andrewgreenwood/scrapbrain/src/panel/graphics.h

#ifndef SCRAPBRAIN_GRAPHICS_H
#define SCRAPBRAIN_GRAPHICS_H 1

#define BACKGROUND_COLOUR           0x1082
#define TOPBAR_COLOUR               0x0000
#define CARRIER_OPERATOR_COLOUR     0x2589
#define MODULATOR_OPERATOR_COLOUR   0xf3e4
#define OPERATOR_LINK_COLOUR        0xffff

#define INDICATOR_OUTLINE_COLOUR    0xffff
#define GREEN_INDICATOR_COLOUR      0x2589
#define GREEN_INDICATOR_LOW_COLOUR  0x0000

#define BUTTON_OUTLINE_COLOUR       BACKGROUND_COLOUR
// 0x0841

enum {
    GRAPHIC_INDICATOR_OUTLINE = GRAPHIC_FIRST_ID,
    GRAPHIC_GREEN_INDICATOR,
    GRAPHIC_ALGORITHM_BUTTON_OUTLINE,
    GRAPHIC_CARRIER_OPERATOR_SQUARE,
    GRAPHIC_BIG_CARRIER_OPERATOR_SQUARE,
    GRAPHIC_MODULATOR_OPERATOR_SQUARE,
    GRAPHIC_BIG_MODULATOR_OPERATOR_SQUARE,
    GRAPHIC_VERTICAL_OPERATOR_CONNECTION,
    GRAPHIC_BIG_VERTICAL_OPERATOR_CONNECTION,
    GRAPHIC_UP_LEFT_OPERATOR_CONNECTION,
    GRAPHIC_BIG_UP_LEFT_OPERATOR_CONNECTION,
    GRAPHIC_UP_RIGHT_OPERATOR_CONNECTION,
    GRAPHIC_BIG_UP_RIGHT_OPERATOR_CONNECTION,
    GRAPHIC_LEFT_UP_OPERATOR_CONNECTION,
    GRAPHIC_BIG_LEFT_UP_OPERATOR_CONNECTION,
    GRAPHIC_RIGHT_UP_OPERATOR_CONNECTION,
    GRAPHIC_BIG_RIGHT_UP_OPERATOR_CONNECTION,
    GRAPHIC_ALGORITHM_1_SMALL,
    GRAPHIC_ALGORITHM_1_BIG,
    GRAPHIC_ALGORITHM_2_SMALL,
    GRAPHIC_ALGORITHM_2_BIG,
    GRAPHIC_ALGORITHM_3_SMALL,
    GRAPHIC_ALGORITHM_3_BIG,
    GRAPHIC_ALGORITHM_4_SMALL,
    GRAPHIC_ALGORITHM_4_BIG,
    GRAPHIC_ALGORITHM_5_SMALL,
    GRAPHIC_ALGORITHM_5_BIG,
    GRAPHIC_ALGORITHM_6_SMALL,
    GRAPHIC_ALGORITHM_6_BIG,
    GRAPHIC_ALGORITHM_7_SMALL,
    GRAPHIC_ALGORITHM_7_BIG,
    GRAPHIC_ALGORITHM_8_SMALL,
    GRAPHIC_ALGORITHM_8_BIG,
    GRAPHIC_FOLDER_IMAGE,
    GRAPHIC_COG_IMAGE,
    GRAPHIC_BOX_IMAGE,
    GRAPHIC_UP_ARROW_IMAGE,
    GRAPHIC_DOWN_ARROW_IMAGE,
    GRAPHIC_RESET_ARROW_IMAGE,
    GRAPHIC_OPEN_FOLDER_IMAGE,
    GRAPHIC_MIDI_CONNECTOR,
    GRAPHIC_LEFT_CHEVRON,
    GRAPHIC_RIGHT_CHEVRON,
    GRAPHIC_SMALL_BUTTON_OUTLINE,
    GRAPHIC_ALGORITHM_SELECT
};

BEGIN_GRAPHIC(graphicIndicatorOutlineData)
    GRAPHIC_SET_COLOUR(0xffff)
    GRAPHIC_HORIZONTAL_LINE(0, 1, 5)
    GRAPHIC_HORIZONTAL_LINE(6, 1, 5)
    GRAPHIC_VERTICAL_LINE(0, 1, 5)
    GRAPHIC_VERTICAL_LINE(6, 1, 5)
END_GRAPHIC()

BEGIN_GRAPHIC(graphicGreenIndicatorData)
    GRAPHIC_SET_COLOUR(GREEN_INDICATOR_COLOUR)
    GRAPHIC_FILLED_SQUARE(1, 1, 3)
    GRAPHIC_HORIZONTAL_LINE(0, 0, 4)
    GRAPHIC_VERTICAL_LINE(0, 1, 4)
    GRAPHIC_SET_COLOUR(GREEN_INDICATOR_LOW_COLOUR)
    GRAPHIC_HORIZONTAL_LINE(4, 1, 4)
    GRAPHIC_VERTICAL_LINE(4, 1, 3)
END_GRAPHIC()

BEGIN_GRAPHIC(graphicAlgorithmButtonOutlineData)
    GRAPHIC_SET_COLOUR(BUTTON_OUTLINE_COLOUR)
    GRAPHIC_SQUARE(0, 0, 45)
END_GRAPHIC()

BEGIN_GRAPHIC(graphicCarrierOperatorSquareData)
    GRAPHIC_SET_COLOUR(CARRIER_OPERATOR_COLOUR)
    GRAPHIC_SQUARE(0, 0, 7)
END_GRAPHIC()

BEGIN_GRAPHIC(graphicBigCarrierOperatorSquareData)
    GRAPHIC_SET_COLOUR(CARRIER_OPERATOR_COLOUR)
    GRAPHIC_SQUARE(0, 0, 30)
    GRAPHIC_SQUARE(1, 1, 28)
END_GRAPHIC()

BEGIN_GRAPHIC(graphicModulatorOperatorSquareData)
    GRAPHIC_SET_COLOUR(MODULATOR_OPERATOR_COLOUR)
    GRAPHIC_SQUARE(0, 0, 7)
END_GRAPHIC()

BEGIN_GRAPHIC(graphicBigModulatorOperatorSquareData)
    GRAPHIC_SET_COLOUR(MODULATOR_OPERATOR_COLOUR)
    GRAPHIC_SQUARE(0, 0, 30)
    GRAPHIC_SQUARE(1, 1, 28)
END_GRAPHIC()

BEGIN_GRAPHIC(graphicVerticalOperatorConnectionData)
    GRAPHIC_SET_COLOUR(OPERATOR_LINK_COLOUR)
    GRAPHIC_VERTICAL_LINE(0, 0, 2)
END_GRAPHIC()

BEGIN_GRAPHIC(graphicBigVerticalOperatorConnectionData)
    GRAPHIC_SET_COLOUR(OPERATOR_LINK_COLOUR)
    GRAPHIC_FILLED_RECTANGLE(0, 0, 3, 10)
END_GRAPHIC()

BEGIN_GRAPHIC(graphicUpLeftOperatorConnectionData)
    GRAPHIC_SET_COLOUR(OPERATOR_LINK_COLOUR)
    GRAPHIC_VERTICAL_LINE(3, 1, 5)
    GRAPHIC_HORIZONTAL_LINE(0, 0, 2)
END_GRAPHIC()

BEGIN_GRAPHIC(graphicBigUpLeftOperatorConnectionData)
    GRAPHIC_SET_COLOUR(OPERATOR_LINK_COLOUR)
    GRAPHIC_FILLED_RECTANGLE(0, 0, 16, 3)
    GRAPHIC_FILLED_RECTANGLE(14, 1, 3, 22)
END_GRAPHIC()

BEGIN_GRAPHIC(graphicUpRightOperatorConnectionData)
    GRAPHIC_SET_COLOUR(OPERATOR_LINK_COLOUR)
    GRAPHIC_VERTICAL_LINE(0, 1, 5)
    GRAPHIC_HORIZONTAL_LINE(0, 1, 3)
END_GRAPHIC()

BEGIN_GRAPHIC(graphicBigUpRightOperatorConnectionData)
    GRAPHIC_SET_COLOUR(OPERATOR_LINK_COLOUR)
    GRAPHIC_FILLED_RECTANGLE(1, 0, 15, 3)
    GRAPHIC_FILLED_RECTANGLE(0, 1, 3, 22)
END_GRAPHIC()

BEGIN_GRAPHIC(graphicLeftUpOperatorConnectionData)
    GRAPHIC_SET_COLOUR(OPERATOR_LINK_COLOUR)
    GRAPHIC_HORIZONTAL_LINE(5, 1, 6)
    GRAPHIC_VERTICAL_LINE(0, 0, 4)
END_GRAPHIC()

BEGIN_GRAPHIC(graphicBigLeftUpOperatorConnectionData)
    GRAPHIC_SET_COLOUR(OPERATOR_LINK_COLOUR)
    GRAPHIC_FILLED_RECTANGLE(1, 20, 26, 3)
    GRAPHIC_FILLED_RECTANGLE(0, 0, 3, 22)
END_GRAPHIC()

BEGIN_GRAPHIC(graphicRightUpOperatorConnectionData)
    GRAPHIC_SET_COLOUR(OPERATOR_LINK_COLOUR)
    GRAPHIC_HORIZONTAL_LINE(5, 0, 5)
    GRAPHIC_VERTICAL_LINE(6, 0, 4)
END_GRAPHIC()

BEGIN_GRAPHIC(graphicBigRightUpOperatorConnectionData)
    GRAPHIC_SET_COLOUR(OPERATOR_LINK_COLOUR)
    GRAPHIC_FILLED_RECTANGLE(0, 20, 26, 3)
    GRAPHIC_FILLED_RECTANGLE(24, 0, 3, 22)
END_GRAPHIC()

BEGIN_GRAPHIC(graphicAlgorithm1SmallData)
    GRAPHIC(GRAPHIC_CARRIER_OPERATOR_SQUARE, 17, 2)
    GRAPHIC(GRAPHIC_MODULATOR_OPERATOR_SQUARE, 17, 12)
    GRAPHIC(GRAPHIC_MODULATOR_OPERATOR_SQUARE, 17, 22)
    GRAPHIC(GRAPHIC_MODULATOR_OPERATOR_SQUARE, 17, 32)
    GRAPHIC(GRAPHIC_VERTICAL_OPERATOR_CONNECTION, 20, 9)
    GRAPHIC(GRAPHIC_VERTICAL_OPERATOR_CONNECTION, 20, 19)
    GRAPHIC(GRAPHIC_VERTICAL_OPERATOR_CONNECTION, 20, 29)
END_GRAPHIC()

BEGIN_GRAPHIC(graphicAlgorithm1BigData)
    GRAPHIC_SET_TEXT_SIZE(2)
    GRAPHIC(GRAPHIC_BIG_CARRIER_OPERATOR_SQUARE, 60, 0)
    GRAPHIC_CHARACTER(70, 8, '4')
    GRAPHIC(GRAPHIC_BIG_MODULATOR_OPERATOR_SQUARE, 60, 40)
    GRAPHIC_CHARACTER(70, 48, '3')
    GRAPHIC(GRAPHIC_BIG_MODULATOR_OPERATOR_SQUARE, 60, 80)
    GRAPHIC_CHARACTER(70, 88, '2')
    GRAPHIC(GRAPHIC_BIG_MODULATOR_OPERATOR_SQUARE, 60, 120)
    GRAPHIC_CHARACTER(70, 128, '1')
    GRAPHIC(GRAPHIC_BIG_VERTICAL_OPERATOR_CONNECTION, 74, 30)
    GRAPHIC(GRAPHIC_BIG_VERTICAL_OPERATOR_CONNECTION, 74, 70)
    GRAPHIC(GRAPHIC_BIG_VERTICAL_OPERATOR_CONNECTION, 74, 110)
END_GRAPHIC()

BEGIN_GRAPHIC(graphicAlgorithm2SmallData)
    GRAPHIC(GRAPHIC_CARRIER_OPERATOR_SQUARE, 17, 7)
    GRAPHIC(GRAPHIC_MODULATOR_OPERATOR_SQUARE, 17, 17)
    GRAPHIC(GRAPHIC_MODULATOR_OPERATOR_SQUARE, 10, 27)
    GRAPHIC(GRAPHIC_MODULATOR_OPERATOR_SQUARE, 24, 27)
    GRAPHIC(GRAPHIC_VERTICAL_OPERATOR_CONNECTION, 20, 14)
    GRAPHIC(GRAPHIC_UP_RIGHT_OPERATOR_CONNECTION, 13, 21)
    GRAPHIC(GRAPHIC_UP_LEFT_OPERATOR_CONNECTION, 24, 21)
END_GRAPHIC()

BEGIN_GRAPHIC(graphicAlgorithm2BigData)
    GRAPHIC_SET_TEXT_SIZE(2)
    GRAPHIC(GRAPHIC_BIG_CARRIER_OPERATOR_SQUARE, 60, 20)
    GRAPHIC_CHARACTER(70, 28, '4')
    GRAPHIC(GRAPHIC_BIG_MODULATOR_OPERATOR_SQUARE, 60, 60)
    GRAPHIC_CHARACTER(70, 68, '3')
    GRAPHIC(GRAPHIC_BIG_MODULATOR_OPERATOR_SQUARE, 30, 100)
    GRAPHIC_CHARACTER(40, 108, '1')
    GRAPHIC(GRAPHIC_BIG_MODULATOR_OPERATOR_SQUARE, 90, 100)
    GRAPHIC_CHARACTER(100, 108, '2')
    GRAPHIC(GRAPHIC_BIG_VERTICAL_OPERATOR_CONNECTION, 74, 50)
    GRAPHIC(GRAPHIC_BIG_UP_RIGHT_OPERATOR_CONNECTION, 44, 77)
    GRAPHIC(GRAPHIC_BIG_UP_LEFT_OPERATOR_CONNECTION, 90, 77)
END_GRAPHIC()

BEGIN_GRAPHIC(graphicAlgorithm3SmallData)
    GRAPHIC(GRAPHIC_CARRIER_OPERATOR_SQUARE, 17, 7)
    GRAPHIC(GRAPHIC_MODULATOR_OPERATOR_SQUARE, 10, 17)
    GRAPHIC(GRAPHIC_MODULATOR_OPERATOR_SQUARE, 24, 17)
    GRAPHIC(GRAPHIC_MODULATOR_OPERATOR_SQUARE, 24, 27)
    GRAPHIC(GRAPHIC_UP_RIGHT_OPERATOR_CONNECTION, 13, 11)
    GRAPHIC(GRAPHIC_UP_LEFT_OPERATOR_CONNECTION, 24, 11)
    GRAPHIC(GRAPHIC_VERTICAL_OPERATOR_CONNECTION, 27, 24)
END_GRAPHIC()

BEGIN_GRAPHIC(graphicAlgorithm3BigData)
    GRAPHIC_SET_TEXT_SIZE(2)
    GRAPHIC(GRAPHIC_BIG_CARRIER_OPERATOR_SQUARE, 60, 20)
    GRAPHIC_CHARACTER(70, 28, '4')
    GRAPHIC(GRAPHIC_BIG_MODULATOR_OPERATOR_SQUARE, 30, 60)
    GRAPHIC_CHARACTER(40, 68, '1')
    GRAPHIC(GRAPHIC_BIG_MODULATOR_OPERATOR_SQUARE, 90, 60)
    GRAPHIC_CHARACTER(100, 68, '3')
    GRAPHIC(GRAPHIC_BIG_MODULATOR_OPERATOR_SQUARE, 90, 100)
    GRAPHIC_CHARACTER(100, 108, '2')
    GRAPHIC(GRAPHIC_BIG_UP_RIGHT_OPERATOR_CONNECTION, 44, 37)
    GRAPHIC(GRAPHIC_BIG_UP_LEFT_OPERATOR_CONNECTION, 90, 37)
    GRAPHIC(GRAPHIC_BIG_VERTICAL_OPERATOR_CONNECTION, 104, 90)
END_GRAPHIC()

BEGIN_GRAPHIC(graphicAlgorithm4SmallData)
    GRAPHIC(GRAPHIC_CARRIER_OPERATOR_SQUARE, 17, 7)
    GRAPHIC(GRAPHIC_MODULATOR_OPERATOR_SQUARE, 10, 17)
    GRAPHIC(GRAPHIC_MODULATOR_OPERATOR_SQUARE, 24, 17)
    GRAPHIC(GRAPHIC_MODULATOR_OPERATOR_SQUARE, 10, 27)
    GRAPHIC(GRAPHIC_UP_RIGHT_OPERATOR_CONNECTION, 13, 11)
    GRAPHIC(GRAPHIC_UP_LEFT_OPERATOR_CONNECTION, 24, 11)
    GRAPHIC(GRAPHIC_VERTICAL_OPERATOR_CONNECTION, 13, 24)
END_GRAPHIC()

BEGIN_GRAPHIC(graphicAlgorithm4BigData)
    GRAPHIC_SET_TEXT_SIZE(2)
    GRAPHIC(GRAPHIC_BIG_CARRIER_OPERATOR_SQUARE, 60, 20)
    GRAPHIC_CHARACTER(70, 28, '4')
    GRAPHIC(GRAPHIC_BIG_MODULATOR_OPERATOR_SQUARE, 30, 60)
    GRAPHIC_CHARACTER(40, 68, '2')
    GRAPHIC(GRAPHIC_BIG_MODULATOR_OPERATOR_SQUARE, 90, 60)
    GRAPHIC_CHARACTER(100, 68, '3')
    GRAPHIC(GRAPHIC_BIG_MODULATOR_OPERATOR_SQUARE, 30, 100)
    GRAPHIC_CHARACTER(40, 108, '1')
    GRAPHIC(GRAPHIC_BIG_UP_RIGHT_OPERATOR_CONNECTION, 44, 37)
    GRAPHIC(GRAPHIC_BIG_UP_LEFT_OPERATOR_CONNECTION, 90, 37)
    GRAPHIC(GRAPHIC_BIG_VERTICAL_OPERATOR_CONNECTION, 44, 90)
END_GRAPHIC()

BEGIN_GRAPHIC(graphicAlgorithm5SmallData)
    GRAPHIC(GRAPHIC_CARRIER_OPERATOR_SQUARE, 12, 12)
    GRAPHIC(GRAPHIC_CARRIER_OPERATOR_SQUARE, 22, 12)
    GRAPHIC(GRAPHIC_MODULATOR_OPERATOR_SQUARE, 12, 22)
    GRAPHIC(GRAPHIC_MODULATOR_OPERATOR_SQUARE, 22, 22)
    GRAPHIC(GRAPHIC_VERTICAL_OPERATOR_CONNECTION, 15, 19)
    GRAPHIC(GRAPHIC_VERTICAL_OPERATOR_CONNECTION, 25, 19)
END_GRAPHIC()

BEGIN_GRAPHIC(graphicAlgorithm5BigData)
    GRAPHIC_SET_TEXT_SIZE(2)
    GRAPHIC(GRAPHIC_BIG_CARRIER_OPERATOR_SQUARE, 40, 40)
    GRAPHIC_CHARACTER(50, 48, '2')
    GRAPHIC(GRAPHIC_BIG_CARRIER_OPERATOR_SQUARE, 80, 40)
    GRAPHIC_CHARACTER(90, 48, '4')
    GRAPHIC(GRAPHIC_BIG_MODULATOR_OPERATOR_SQUARE, 40, 80)
    GRAPHIC_CHARACTER(50, 88, '1')
    GRAPHIC(GRAPHIC_BIG_MODULATOR_OPERATOR_SQUARE, 80, 80)
    GRAPHIC_CHARACTER(90, 88, '3')
    GRAPHIC(GRAPHIC_BIG_VERTICAL_OPERATOR_CONNECTION, 54, 70)
    GRAPHIC(GRAPHIC_BIG_VERTICAL_OPERATOR_CONNECTION, 94, 70)
END_GRAPHIC()

BEGIN_GRAPHIC(graphicAlgorithm6SmallData)
    GRAPHIC(GRAPHIC_CARRIER_OPERATOR_SQUARE, 7, 12)
    GRAPHIC(GRAPHIC_CARRIER_OPERATOR_SQUARE, 17, 12)
    GRAPHIC(GRAPHIC_CARRIER_OPERATOR_SQUARE, 27, 12)
    GRAPHIC(GRAPHIC_MODULATOR_OPERATOR_SQUARE, 17, 22)
    GRAPHIC(GRAPHIC_LEFT_UP_OPERATOR_CONNECTION, 10, 19)
    GRAPHIC(GRAPHIC_VERTICAL_OPERATOR_CONNECTION, 20, 19)
    GRAPHIC(GRAPHIC_RIGHT_UP_OPERATOR_CONNECTION, 24, 19)
END_GRAPHIC()

BEGIN_GRAPHIC(graphicAlgorithm6BigData)
    GRAPHIC_SET_TEXT_SIZE(2)
    GRAPHIC(GRAPHIC_BIG_CARRIER_OPERATOR_SQUARE, 20, 40)
    GRAPHIC_CHARACTER(30, 48, '2')
    GRAPHIC(GRAPHIC_BIG_CARRIER_OPERATOR_SQUARE, 60, 40)
    GRAPHIC_CHARACTER(70, 48, '3')
    GRAPHIC(GRAPHIC_BIG_CARRIER_OPERATOR_SQUARE, 100, 40)
    GRAPHIC_CHARACTER(110, 48, '4')
    GRAPHIC(GRAPHIC_BIG_MODULATOR_OPERATOR_SQUARE, 60, 80)
    GRAPHIC_CHARACTER(70, 88, '1')
    GRAPHIC(GRAPHIC_BIG_VERTICAL_OPERATOR_CONNECTION, 74, 70)
    GRAPHIC(GRAPHIC_BIG_LEFT_UP_OPERATOR_CONNECTION, 33, 70)
    GRAPHIC(GRAPHIC_BIG_RIGHT_UP_OPERATOR_CONNECTION, 90, 70)
END_GRAPHIC()

BEGIN_GRAPHIC(graphicAlgorithm7SmallData)
    GRAPHIC(GRAPHIC_CARRIER_OPERATOR_SQUARE, 7, 12)
    GRAPHIC(GRAPHIC_CARRIER_OPERATOR_SQUARE, 17, 12)
    GRAPHIC(GRAPHIC_CARRIER_OPERATOR_SQUARE, 27, 12)
    GRAPHIC(GRAPHIC_MODULATOR_OPERATOR_SQUARE, 7, 22)
    GRAPHIC(GRAPHIC_VERTICAL_OPERATOR_CONNECTION, 10, 19)
END_GRAPHIC()

BEGIN_GRAPHIC(graphicAlgorithm7BigData)
    GRAPHIC_SET_TEXT_SIZE(2)
    GRAPHIC(GRAPHIC_BIG_CARRIER_OPERATOR_SQUARE, 20, 40)
    GRAPHIC_CHARACTER(30, 48, '2')
    GRAPHIC(GRAPHIC_BIG_CARRIER_OPERATOR_SQUARE, 60, 40)
    GRAPHIC_CHARACTER(70, 48, '3')
    GRAPHIC(GRAPHIC_BIG_CARRIER_OPERATOR_SQUARE, 100, 40)
    GRAPHIC_CHARACTER(110, 48, '4')
    GRAPHIC(GRAPHIC_BIG_MODULATOR_OPERATOR_SQUARE, 20, 80)
    GRAPHIC_CHARACTER(30, 88, '1')
    GRAPHIC(GRAPHIC_BIG_VERTICAL_OPERATOR_CONNECTION, 34, 70)
END_GRAPHIC()

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
        0x88, 0x00, 0x00, 0x20,
        0x90, 0x00, 0x00, 0x40,
        0x90, 0x00, 0x00, 0x40,
        0xa0, 0x00, 0x00, 0x80,
        0xa0, 0x00, 0x00, 0x80,
        0xc0, 0x00, 0x01, 0x00,
        0x40, 0x00, 0x01, 0x00,
        0x3f, 0xff, 0xfe, 0x00
    )
END_GRAPHIC()

BEGIN_GRAPHIC(midiConnectorGraphic)
    //GRAPHIC_SET_COLOUR(COLOUR_YELLOW)
    GRAPHIC_BITMAP(0, 0, 32, 33,
        0x00, 0x0f, 0xf0, 0x00,
        0x00, 0x37, 0xec, 0x00,
        0x00, 0xc7, 0xe3, 0x00,
        0x03, 0x07, 0xe0, 0xc0,
        0x04, 0x07, 0xe0, 0x20,
        0x08, 0x00, 0x00, 0x10,
        0x08, 0x00, 0x00, 0x08,
        0x10, 0x00, 0x00, 0x08,
        0x20, 0x00, 0x00, 0x04,
        0x20, 0x00, 0x00, 0x04,
        0x40, 0x00, 0x00, 0x02,
        0x40, 0x00, 0x00, 0x02,
        0x40, 0x00, 0x00, 0x02,
        0x80, 0x00, 0x00, 0x01,
        0x80, 0x00, 0x00, 0x01,
        0x80, 0x00, 0x00, 0x01,
        0x83, 0x00, 0x00, 0xc1,
        0x83, 0x00, 0x00, 0xc1,
        0x80, 0x00, 0x00, 0x01,
        0x80, 0x00, 0x00, 0x01,
        0x40, 0x00, 0x00, 0x02,
        0x40, 0x00, 0x00, 0x02,
        0x40, 0x60, 0x06, 0x02,
        0x20, 0x60, 0x06, 0x04,
        0x20, 0x00, 0x00, 0x04,
        0x10, 0x01, 0x80, 0x08,
        0x08, 0x01, 0x80, 0x08,
        0x08, 0x00, 0x00, 0x10,
        0x04, 0x00, 0x00, 0x20,
        0x03, 0x00, 0x00, 0xc0,
        0x00, 0xc0, 0x03, 0x00,
        0x00, 0x30, 0x0c, 0x00,
        0x00, 0x0f, 0xf0, 0x00
    )
END_GRAPHIC()

BEGIN_GRAPHIC(leftChevronGraphic)
    GRAPHIC_BITMAP(0, 0, 8, 14,
        0x03,
        0x07,
        0x0e,
        0x1c,
        0x38,
        0x70,
        0xe0,
        0xe0,
        0x70,
        0x38,
        0x1c,
        0x0e,
        0x07,
        0x03
    )
END_GRAPHIC()

BEGIN_GRAPHIC(rightChevronGraphic)
    GRAPHIC_BITMAP(0, 0, 8, 14,
        0xc0,
        0xe0,
        0x70,
        0x38,
        0x1c,
        0x0e,
        0x07,
        0x07,
        0x0e,
        0x1c,
        0x38,
        0x70,
        0xe0,
        0xc0
    )
END_GRAPHIC()

BEGIN_GRAPHIC(smallButtonOutlineGraphic)
    GRAPHIC_SET_COLOUR(COLOUR_WHITE)        // TODO
    GRAPHIC_VERTICAL_LINE(0, 2, 23)
    GRAPHIC_HORIZONTAL_LINE(0, 2, 23)
    GRAPHIC_VERTICAL_LINE(25, 2, 23)
    GRAPHIC_HORIZONTAL_LINE(25, 2, 23)
    GRAPHIC_PIXEL(1, 1)
    GRAPHIC_PIXEL(24, 1)
    GRAPHIC_PIXEL(1, 24)
    GRAPHIC_PIXEL(24, 24)
END_GRAPHIC()

BEGIN_GRAPHIC(algorithmSelectGraphic)
    GRAPHIC_SET_COLOUR(COLOUR_WHITE)        // TODO
    GRAPHIC_VERTICAL_LINE(0, 0, 5)
    GRAPHIC_HORIZONTAL_LINE(0, 1, 5)
    GRAPHIC_VERTICAL_LINE(36, 0, 5)
    GRAPHIC_HORIZONTAL_LINE(0, 31, 35)
    GRAPHIC_VERTICAL_LINE(0, 31, 36)
    GRAPHIC_HORIZONTAL_LINE(36, 1, 5)
    GRAPHIC_VERTICAL_LINE(36, 31, 36)
    GRAPHIC_HORIZONTAL_LINE(36, 31, 35)
END_GRAPHIC()

const uint8_t* const graphics[] PROGMEM = {
    graphicIndicatorOutlineData,
    graphicGreenIndicatorData,
    graphicAlgorithmButtonOutlineData,
    graphicCarrierOperatorSquareData,
    graphicBigCarrierOperatorSquareData,
    graphicModulatorOperatorSquareData,
    graphicBigModulatorOperatorSquareData,
    graphicVerticalOperatorConnectionData,
    graphicBigVerticalOperatorConnectionData,
    graphicUpLeftOperatorConnectionData,
    graphicBigUpLeftOperatorConnectionData,
    graphicUpRightOperatorConnectionData,
    graphicBigUpRightOperatorConnectionData,
    graphicLeftUpOperatorConnectionData,
    graphicBigLeftUpOperatorConnectionData,
    graphicRightUpOperatorConnectionData,
    graphicBigRightUpOperatorConnectionData,
    graphicAlgorithm1SmallData,
    graphicAlgorithm1BigData,
    graphicAlgorithm2SmallData,
    graphicAlgorithm2BigData,
    graphicAlgorithm3SmallData,
    graphicAlgorithm3BigData,
    graphicAlgorithm4SmallData,
    graphicAlgorithm4BigData,
    graphicAlgorithm5SmallData,
    graphicAlgorithm5BigData,
    graphicAlgorithm6SmallData,
    graphicAlgorithm6BigData,
    graphicAlgorithm7SmallData,
    graphicAlgorithm7BigData,
    graphicAlgorithm8SmallData,
    graphicAlgorithm8BigData,
    folderGraphicData,
    cogGraphicData,
    boxGraphicData,
    arrowUpGraphicData,
    arrowDownGraphicData,
    arrowResetGraphicData,
    folderOpenGraphicData,
    midiConnectorGraphic,
    leftChevronGraphic,
    rightChevronGraphic,
    smallButtonOutlineGraphic,
    algorithmSelectGraphic
};

#endif
